smartc/SkyConditions_90640/Enclosure/Sky Conditions 90640 - Enclosure.3mf

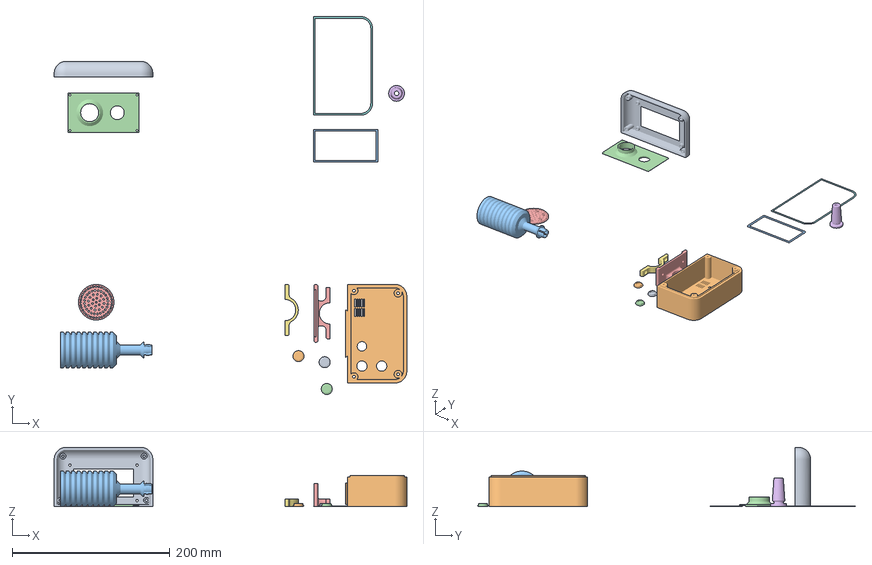
[picture p15: CAD file, 2026-04-03]
Enclosure/Sky Conditions 90640 - Enclosure.3mf
446.8 x 478.9 x 75.0 mm
Housing - Top.stl
Housing - Base.stl
Stevenson Screen.stl
Sensor Insert Plate.stl
Housing - Bracket.stl
TPU Cable Grommet.stl
Housing - Bracket Clamp.stl
TPU Housing Body Gasket.stl
Housing - Plug.stl x 3
TPU Sensor Insert Gasket.stl
Stevenson Screen - Base Cap.stl
