smartc/SkyConditions_90640/Enclosure/TPU Housing Body Gasket.stl

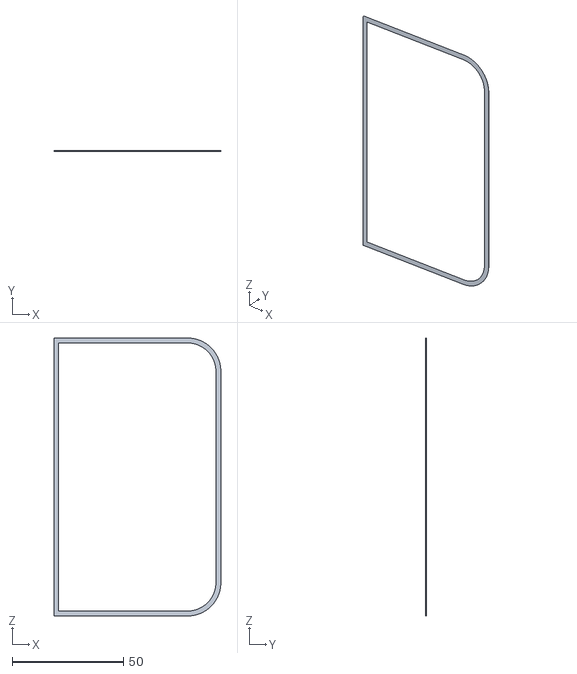
[picture p16: CAD file, 2026-04-03]
Enclosure/TPU Housing Body Gasket.stl
75.0 x 0.5 x 125.0
