smartc/SkyConditions_90640/html_templates.h

#ifndef HTML_TEMPLATES_H
#define HTML_TEMPLATES_H

#include <Arduino.h>
#include <WiFi.h>
#include "config.h"
#include "sky_sensor.h"
#include "config_store.h"
#include "rain_sensor.h"
#include "dht_sensor.h"

// ---------------------------------------------------------------------------
// Shared CSS
// ---------------------------------------------------------------------------
inline String getCommonStyles()
{
  return
    "* { box-sizing: border-box; }\n"
    "body { font-family: Arial, sans-serif; background: #1a1a2e; color: #e0e0e0; margin: 0; padding: 16px; }\n"
    "h1, h2 { color: #a0c4ff; }\n"
    "a { color: #74b9ff; text-decoration: none; }\n"
    "a:hover { text-decoration: underline; }\n"
    ".card { background: #16213e; border-radius: 8px; padding: 16px; margin-bottom: 16px;"
             " box-shadow: 0 2px 8px rgba(0,0,0,0.4); }\n"
    "table { border-collapse: collapse; width: 100%; }\n"
    "th, td { border: 1px solid #2d3561; padding: 8px; text-align: left; }\n"
    "th { background: #0f3460; }\n"
    ".nav { margin-bottom: 16px; }\n"
    ".nav a { display: inline-block; background: #0f3460; color: #e0e0e0; padding: 8px 14px;"
              " border-radius: 4px; margin-right: 8px; }\n"
    ".nav a:hover { background: #16213e; text-decoration: none; }\n"
    ".nav a.warn { background: #7f4f00; }\n"
    ".tbtn { display:inline-block; padding:6px 12px; margin:2px; border-radius:4px;"
             " background:#0f3460; color:#e0e0e0; cursor:pointer; border:none;"
             " font-size:0.85em; }\n"
    ".tbtn:hover { background:#1a4a8a; }\n"
    ".tbtn.act { background:#4a90d9; color:#fff; }\n"
    "#hist-status { font-size:0.8em; color:#636e72; margin-top:8px; }\n"
    ".btn { display: inline-block; padding: 8px 16px; border-radius: 4px; cursor: pointer;"
            " border: none; color: white; }\n"
    ".btn-danger { background: #c0392b; }\n"
    ".btn-danger:hover { background: #96281b; }\n"
    ".stat-grid { display: grid; grid-template-columns: repeat(auto-fit, minmax(140px,1fr));"
                 " gap: 12px; }\n"
    ".stat-box { background: #0f3460; border-radius: 6px; padding: 12px; text-align: center; }\n"
    ".stat-label { font-size: 0.75em; color: #74b9ff; text-transform: uppercase; letter-spacing: 1px; }\n"
    ".stat-value { font-size: 1.6em; font-weight: bold; margin-top: 4px; }\n"
    ".sky-temp  { color: #a29bfe; }\n"
    ".min-temp  { color: #74b9ff; }\n"
    ".max-temp  { color: #fd79a8; }\n"
    ".med-temp  { color: #55efc4; }\n"
    ".amb-temp  { color: #ffeaa7; }\n"
    "#thermal-canvas { display: block; margin: 0 auto; image-rendering: pixelated; border-radius: 4px; }\n"
    "#ws-status { font-size: 0.8em; color: #636e72; margin-top: 6px; text-align: center; }\n";
}

// ---------------------------------------------------------------------------
// Shared page header
// ---------------------------------------------------------------------------
inline String getPageHeader(const String& title)
{
  return
    "<!DOCTYPE html><html>\n"
    "<head><title>" + title + "</title>\n"
    "<meta charset='UTF-8'>\n"
    "<meta name='viewport' content='width=device-width, initial-scale=1'>\n"
    "<style>" + getCommonStyles() + "</style>\n"
    "</head>\n<body>\n";
}

// ---------------------------------------------------------------------------
// Navigation bar
// ---------------------------------------------------------------------------
inline String getNavBar()
{
  return
    "<div class='nav'>\n"
    "<a href='/'>Home</a>\n"
    "<a href='/setup'>Setup</a>\n"
    "<a href='/trends'>Trends</a>\n"
    "<a href='/console'>Console</a>\n"
    "<a href='/update' class='warn'>Update</a>\n"
    "</div>\n";
}

// ---------------------------------------------------------------------------
// Adaptive lux formatter – 1 dp when >= 1 lux, more below that.
// ---------------------------------------------------------------------------
inline String fmtLux(float lux)
{
  if (lux >= 1.0f)    return String(lux, 1)  + " lux";
  if (lux >= 0.1f)    return String(lux, 3)  + " lux";
  if (lux >= 0.001f)  return String(lux, 4)  + " lux";
  char buf[24]; snprintf(buf, sizeof(buf), "%.2e lux", lux); return String(buf);
}

// ---------------------------------------------------------------------------
// Home page – live thermal view + reading cards
// ---------------------------------------------------------------------------
inline String getHomePage()
{
  String ip   = WiFi.localIP().toString();
  String host = "ws://" + ip + ":81";

  String html = getPageHeader("Sky Conditions Monitor");
  html += "<h1>Sky Conditions Monitor</h1>\n";
  html += getNavBar();

  // Live thermal canvas
  html += "<div class='card'>\n";
  html += "<h2>Live Thermal View</h2>\n";
  html += "<canvas id='thermal-canvas' width='640' height='480'></canvas>\n";
  html += "<div id='ws-status'>Connecting...</div>\n";
  html += "</div>\n";

  // Temperature statistics
  html += "<div class='card'>\n";
  html += "<h2>Current Readings</h2>\n";
  html += "<div class='stat-grid'>\n";
  html += "  <div class='stat-box'><div class='stat-label'>Sky Temp<br>(center 50% FOV)</div>"
          "    <div class='stat-value sky-temp' id='sky-temp'>--</div></div>\n";
  html += "  <div class='stat-box'><div class='stat-label'>Frame Min</div>"
          "    <div class='stat-value min-temp' id='min-temp'>--</div></div>\n";
  html += "  <div class='stat-box'><div class='stat-label'>Frame Max</div>"
          "    <div class='stat-value max-temp' id='max-temp'>--</div></div>\n";
  html += "  <div class='stat-box'><div class='stat-label'>Frame Median</div>"
          "    <div class='stat-value med-temp' id='med-temp'>--</div></div>\n";
  {
    String ambSrc;
    if      (deviceConfig.dhtType == 5 && dhtData.valid) ambSrc = "BME280";
    else if (deviceConfig.dhtType == 4 && dhtData.valid) ambSrc = "BMP280";
    else if (deviceConfig.dhtType == 3 && dhtData.valid) ambSrc = "BMP180";
    else if (deviceConfig.dhtType && dhtData.valid)      ambSrc = "DHT";
    else                                                  ambSrc = "MLX die";
    html += "  <div class='stat-box'><div class='stat-label'>Ambient<br>"
            "<span style='font-size:0.8em;color:#8899aa' id='amb-src'>" + ambSrc + "</span></div>"
            "    <div class='stat-value amb-temp' id='amb-temp'>" +
            (skyConditions.hasData() ? String(skyConditions.getAmbientTemperature(), 1) + "°C" : "--") +
            "</div></div>\n";
  }
  if ((deviceConfig.dhtType >= 1 && deviceConfig.dhtType <= 2) || deviceConfig.dhtType == 5) {
    // Humidity available from DHT11/DHT22 and BME280
    const char *humSrc = (deviceConfig.dhtType == 5) ? "BME280" : "DHT";
    String humVal = dhtData.valid ? String(dhtData.humidity, 0) + "%" : "--";
    html += "  <div class='stat-box'><div class='stat-label'>Humidity<br>"
            "<span style='font-size:0.8em;color:#8899aa'>" + String(humSrc) + "</span></div>"
            "    <div class='stat-value' id='hum-val' style='color:#74b9ff'>" + humVal + "</div></div>\n";
  }
  if (deviceConfig.dhtType == 3 || deviceConfig.dhtType == 4 || deviceConfig.dhtType == 5) {
    // Pressure available from BMP180/BMP280/BME280
    const char *presSrc = (deviceConfig.dhtType == 5) ? "BME280"
                        : (deviceConfig.dhtType == 4) ? "BMP280" : "BMP180";
    String presVal = dhtData.valid ? String(dhtData.pressure, 1) + " hPa" : "--";
    html += "  <div class='stat-box'><div class='stat-label'>Pressure<br>"
            "<span style='font-size:0.8em;color:#8899aa'>" + String(presSrc) + "</span></div>"
            "    <div class='stat-value' id='pres-val' style='color:#74b9ff'>" + presVal + "</div></div>\n";
  }
  html += "  <div class='stat-box'><div class='stat-label'>Cloud Cover<br><span style='font-size:0.8em;color:#74b9ff'>Mean</span></div>"
          "    <div class='stat-value' id='cloud-mean' style='color:#dfe6e9'>" +
          (skyConditions.hasData() ? String(skyConditions.getCloudCoverMean(), 0) + "%" : "--") +
          "</div></div>\n";
  html += "  <div class='stat-box'><div class='stat-label'>Cloud Cover<br><span style='font-size:0.8em;color:#74b9ff'>Per-Pixel</span></div>"
          "    <div class='stat-value' id='cloud-px' style='color:#b2bec3'>" +
          (skyConditions.hasData() ? String(skyConditions.getCloudCoverPixel(), 0) + "%" : "--") +
          "</div></div>\n";
  html += "  <div class='stat-box'><div class='stat-label'>Sky Brightness</div>"
          "    <div class='stat-value' id='lux-val' style='color:#fdcb6e'>" +
          (skyConditions.hasBrightnessData() ? fmtLux(skyConditions.getLux()) : "--") +
          "</div></div>\n";
  html += "  <div class='stat-box'><div class='stat-label'>Sky Quality</div>"
          "    <div class='stat-value' id='sqm-val' style='color:#00cec9'>" +
          (skyConditions.hasBrightnessData() ? String(skyConditions.getSqm(), 2) + " mag/\"²" : "--") +
          "</div></div>\n";
  {
    bool enabled     = deviceConfig.rainEnabled;
    bool wet         = rainIsWet();
    bool relayMode   = (deviceConfig.rainMode == 0);
    String mainColor = !enabled ? "#636e72" : (wet ? "#74b9ff" : "#00b894");
    String mainLabel = !enabled ? "--"       : (wet ? "WET"     : "DRY");
    String subTxt;
    if (!enabled) {
      subTxt = "Disabled";
    } else if (relayMode) {
      subTxt = rainData.relayWet ? "Relay: WET" : "Relay: DRY";
    } else {
      subTxt = rainData.modbusOk
               ? (rainData.modbusWet ? "RS485: WET" : "RS485: DRY")
               : "RS485: --";
    }
    // IDs are used by the WebSocket text-message handler for live relay updates.
    html += "  <div class='stat-box'><div class='stat-label'>Rain / Snow<br>"
            "<span style='font-size:0.8em;color:#8899aa'>" +
            String(relayMode ? "Relay" : "RS485") + "</span></div>"
            "    <div class='stat-value' id='rain-state' style='color:" + mainColor + "'>" + mainLabel + "</div>"
            "    <div id='rain-sub' style='font-size:0.65em;color:#b2bec3;margin-top:4px'>" + subTxt + "</div></div>\n";
  }
  html += "</div>\n";  // stat-grid
  html += "</div>\n";  // card

  // Thermal snapshot image (auto-refreshes every JPEG_INTERVAL_MS)
  html += "<div class='card'>\n";
  html += "<h2>Thermal Snapshot</h2>\n";
  html += "<p style='font-size:0.8em;color:#636e72'>Refreshes every " +
          String(JPEG_INTERVAL_MS / 1000) + " s &nbsp;&middot;&nbsp; "
          "<a href='/thermal.jpg'>direct link</a></p>\n";
  html += "<img id='thermal-snap' src='/thermal.jpg' "
          "style='display:block;margin:0 auto;max-width:100%;border-radius:4px;'>\n";
  html += "</div>\n";

  // Device info
  html += "<div class='card'>\n";
  html += "<h2>Device Information</h2>\n";
  html += "<table><tr><th>Property</th><th>Value</th></tr>\n";
  html += "<tr><td>Device Name</td><td>" + String(DEVICE_NAME)    + "</td></tr>\n";
  html += "<tr><td>Firmware</td><td>"    + String(MANUFACTURER_V) + "</td></tr>\n";
  html += "<tr><td>IP Address</td><td>"  + ip + "</td></tr>\n";
  html += "<tr><td>MAC Address</td><td>" + WiFi.macAddress()        + "</td></tr>\n";
  html += "<tr><td>SSID</td><td>"        + WiFi.SSID()              + "</td></tr>\n";
  html += "<tr><td>Signal</td><td>"      + String(WiFi.RSSI())      + " dBm</td></tr>\n";
  html += "<tr><td>ASCOM Port</td><td>"  + String(ALPACA_PORT)      + "</td></tr>\n";
  html += "<tr><td>Uptime</td><td><span id='uptime' data-s='" +
          String(millis()/1000) + "'></span></td></tr>\n";
  html += "<tr><td>Free Heap</td><td>"   + String(ESP.getFreeHeap()) + " bytes</td></tr>\n";
  html += "</table>\n";
  html += "</div>\n";

  // ---------------------------------------------------------------------------
  // JavaScript – WebSocket client + jet colormap renderer
  // ---------------------------------------------------------------------------

  // Compute the box region that matches the per-pixel cloud cover region.
  // Both cloud cover methods are always computed; the box always tracks the
  // per-pixel region (which equals center FOV when cloudPixelRegion == 0).
  int boxCCS, boxCCE, boxCRS, boxCRE;
  if (deviceConfig.cloudPixelRegion == 1) {
    int edge = (int)deviceConfig.cloudEdgeExclude;
    boxCCS = edge;
    boxCCE = SENSOR_COLS - 1 - edge;
    boxCRS = edge;
    boxCRE = SENSOR_ROWS - 1 - edge;
    if (boxCRS > boxCRE || boxCCS > boxCCE) { // degenerate – fall back
      boxCCS = CENTER_COL_START; boxCCE = CENTER_COL_END;
      boxCRS = CENTER_ROW_START; boxCRE = CENTER_ROW_END;
    }
  } else {
    boxCCS = CENTER_COL_START; boxCCE = CENTER_COL_END;
    boxCRS = CENTER_ROW_START; boxCRE = CENTER_ROW_END;
  }

  html += R"rawjs(
<script>
const COLS = 32, ROWS = 24, PIXELS = 768;
const HEADER = 16;  // bytes: 4×float32 (min, max, median, skyTemp)
const canvas = document.getElementById('thermal-canvas');
const ctx    = canvas.getContext('2d');
const imgData = ctx.createImageData(COLS, ROWS);
const status  = document.getElementById('ws-status');

// ClearDarkSky colormap: t=0 (coldest/clear) → dark navy, t=1 (warmest/overcast) → white
const CDS_STOPS = [
  [0,62,126],[19,83,147],[38,102,166],[78,142,206],[98,162,226],
  [118,182,246],[153,217,217],[173,237,237],[193,193,193],[233,233,233],[250,250,250]
];
function cds(t) {
  if (t <= 0) return CDS_STOPS[0];
  if (t >= 1) return CDS_STOPS[10];
  const lo = Math.floor(t * 10);
  const f  = t * 10 - lo;
  return CDS_STOPS[lo].map((c, i) => Math.round(c + f * (CDS_STOPS[lo+1][i] - c)));
}

// Pre-compute colormap lookup table
const skyLT = new Array(256);
for (let i = 0; i < 256; i++) { skyLT[i] = cds(i/255); }

function fmtLux(lux) {
  if (lux >= 1)     return lux.toFixed(1)       + ' lux';
  if (lux >= 0.1)   return lux.toFixed(3)       + ' lux';
  if (lux >= 0.001) return lux.toFixed(4)       + ' lux';
  return lux.toExponential(2) + ' lux';
}

// Pre-allocate the offscreen source canvas; reused every frame to avoid GC churn.
const srcCanvas = new OffscreenCanvas(COLS, ROWS);
const srcCtx    = srcCanvas.getContext('2d');

let ws, fpsCount = 0, lastFpsTime = Date.now(), fps = 0;

function connect() {
  ws = new WebSocket(')rawjs" + host + R"rawjs(');
  ws.binaryType = 'arraybuffer';

  ws.onopen    = () => { status.textContent = 'Connected'; };
  ws.onclose   = () => { status.textContent = 'Disconnected – reconnecting…';
                          setTimeout(connect, 1500); };
  ws.onerror   = () => { ws.close(); };

  ws.onmessage = (evt) => {
    // Text messages carry JSON status updates.
    if (typeof evt.data === 'string') {
      try {
        const d = JSON.parse(evt.data);
        // Rain state (relay mode live update)
        if (d.rain !== undefined) {
          const wet = d.rain === 'WET';
          const el  = document.getElementById('rain-state');
          const sub = document.getElementById('rain-sub');
          if (el)  { el.textContent = d.rain; el.style.color = wet ? '#74b9ff' : '#00b894'; }
          if (sub) sub.textContent = wet ? 'Relay: WET' : 'Relay: DRY';
        }
        // Sensor state (cloud cover, brightness, ambient)
        if (d.amb !== undefined) {
          const nd = d.has_data, nb = d.has_brightness;
          document.getElementById('amb-temp').textContent   = nd ? d.amb.toFixed(1)        + '°C'        : '--';
          document.getElementById('cloud-mean').textContent = nd ? d.cloud_mean.toFixed(0) + '%'         : '--';
          document.getElementById('cloud-px').textContent   = nd ? d.cloud_px.toFixed(0)   + '%'         : '--';
          document.getElementById('lux-val').textContent    = nb ? fmtLux(d.lux)                         : '--';
          document.getElementById('sqm-val').textContent    = nb ? d.sqm.toFixed(2)        + ' mag/″²'   : '--';
          const humEl = document.getElementById('hum-val');
          if (humEl) humEl.textContent = (d.dht_hum !== undefined) ? d.dht_hum.toFixed(0) + '%' : '--';
        }
      } catch(e) {}
      return;
    }
    // Binary messages are thermal frames.
    const buf  = evt.data;
    if (buf.byteLength < HEADER + PIXELS) return;

    const dv   = new DataView(buf);
    const minT = dv.getFloat32(0,  true);
    const maxT = dv.getFloat32(4,  true);
    const medT = dv.getFloat32(8,  true);
    const skyT = dv.getFloat32(12, true);
    const pix  = new Uint8Array(buf, HEADER, PIXELS);

    // Render pixels
    for (let i = 0; i < PIXELS; i++) {
      const [r,g,b] = skyLT[pix[i]];
      imgData.data[i*4]   = r;
      imgData.data[i*4+1] = g;
      imgData.data[i*4+2] = b;
      imgData.data[i*4+3] = 255;
    }

    // Scale 32×24 → 640×480 with bicubic interpolation to smooth pixels and
    // reduce MLX90640 row/column banding artifacts in the live view.
    srcCtx.putImageData(imgData, 0, 0);
    ctx.imageSmoothingEnabled = true;
    ctx.imageSmoothingQuality = 'high';
    ctx.drawImage(srcCanvas, 0, 0, canvas.width, canvas.height);

    // Draw cloud cover region box
    const ccs = )rawjs" + String(boxCCS) + R"rawjs(,
          cce = )rawjs" + String(boxCCE + 1) + R"rawjs(,
          crs = )rawjs" + String(boxCRS) + R"rawjs(,
          cre = )rawjs" + String(boxCRE + 1) + R"rawjs(;
    const scaleX = canvas.width  / COLS;
    const scaleY = canvas.height / ROWS;
    ctx.strokeStyle = 'rgba(255,60,60,0.85)';
    ctx.lineWidth   = 2;
    ctx.strokeRect(ccs*scaleX, crs*scaleY,
                   (cce-ccs)*scaleX, (cre-crs)*scaleY);

    // Update stat readouts
    document.getElementById('sky-temp').textContent = skyT.toFixed(1) + '°C';
    document.getElementById('min-temp').textContent = minT.toFixed(1) + '°C';
    document.getElementById('max-temp').textContent = maxT.toFixed(1) + '°C';
    document.getElementById('med-temp').textContent = medT.toFixed(1) + '°C';

    // FPS
    fpsCount++;
    const now = Date.now();
    if (now - lastFpsTime >= 1000) {
      fps = fpsCount;
      fpsCount = 0;
      lastFpsTime = now;
    }
    status.textContent =
      'Live – ' + fps + ' fps | Sky: ' + skyT.toFixed(1) +
      '°C | Min: ' + minT.toFixed(1) + '°C | Max: ' + maxT.toFixed(1) + '°C';
  };
}

connect();

// Real-time uptime counter.
(function() {
  const el = document.getElementById('uptime');
  if (!el) return;
  let sec = parseInt(el.dataset.s, 10);
  function fmt(s) {
    const d = Math.floor(s / 86400);
    const h = Math.floor(s % 86400 / 3600);
    const m = Math.floor(s % 3600 / 60);
    const ss = s % 60;
    if (d > 0) return d + 'd ' + h + 'h ' + m + 'm';
    if (h > 0) return h + 'h ' + m + 'm ' + ss + 's';
    return m + 'm ' + ss + 's';
  }
  el.textContent = fmt(sec);
  setInterval(function() { el.textContent = fmt(++sec); }, 1000);
})();

// Auto-refresh the static JPEG snapshot.
setInterval(() => {
  const img = document.getElementById('thermal-snap');
  if (img) img.src = '/thermal.jpg?' + Date.now();
}, )rawjs" + String(JPEG_INTERVAL_MS) + R"rawjs();
</script>
)rawjs";

  html += "</body></html>";
  return html;
}

// ---------------------------------------------------------------------------
// Setup page
// ---------------------------------------------------------------------------
inline String getSetupPage()
{
  String html = getPageHeader("Sky Conditions Setup");
  html += "<h1>Sky Conditions Setup</h1>\n";
  html += getNavBar();

  // Current readings snapshot
  html += "<div class='card'>\n";
  html += "<h2>Current Status</h2>\n";
  html += "<table><tr><th>Property</th><th>Value</th></tr>\n";
  if (skyConditions.hasData()) {
    html += "<tr><td>Sky Temperature (center 50% FOV)</td><td>" +
            String(skyConditions.getSkyTemperature(), 2) + " °C</td></tr>\n";
    html += "<tr><td>Frame Minimum</td><td>" +
            String(skyConditions.getMinTemperature(), 2) + " °C</td></tr>\n";
    html += "<tr><td>Frame Maximum</td><td>" +
            String(skyConditions.getMaxTemperature(), 2) + " °C</td></tr>\n";
    html += "<tr><td>Frame Median</td><td>" +
            String(skyConditions.getMedianTemperature(), 2) + " °C</td></tr>\n";
    html += "<tr><td>Ambient (die temp)</td><td>" +
            String(skyConditions.getAmbientTemperature(), 2) + " °C</td></tr>\n";
    unsigned long ageSec = (millis() - skyConditions.getLastUpdateMillis()) / 1000;
    html += "<tr><td>Last Update (thermal)</td><td>" + String(ageSec) + " s ago</td></tr>\n";
  } else {
    html += "<tr><td colspan='2'>No sensor data yet</td></tr>\n";
  }
  if (skyConditions.hasBrightnessData()) {
    html += "<tr><td>Sky Brightness</td><td>" +
            String(skyConditions.getLux(), 4) + " lux</td></tr>\n";
    html += "<tr><td>Sky Quality</td><td>" +
            String(skyConditions.getSqm(), 2) + " mag/arcsec\u00B2</td></tr>\n";
    unsigned long bAgeSec = (millis() - skyConditions.getLastBrightnessMillis()) / 1000;
    html += "<tr><td>Last Update (brightness)</td><td>" + String(bAgeSec) + " s ago</td></tr>\n";
  } else {
    html += "<tr><td>Sky Brightness</td><td>No TSL2591 data yet</td></tr>\n";
  }
  html += "</table>\n";
  html += "</div>\n";

  // ASCOM information
  html += "<div class='card'>\n";
  html += "<h2>ASCOM Alpaca</h2>\n";
  html += "<table><tr><th>Property</th><th>Value</th></tr>\n";
  html += "<tr><td>Device Type</td><td>ObservingConditions</td></tr>\n";
  html += "<tr><td>Device Number</td><td>0</td></tr>\n";
  html += "<tr><td>Alpaca Port</td><td>" + String(ALPACA_PORT) + "</td></tr>\n";
  html += "<tr><td>Discovery Port</td><td>" + String(ALPACA_DISCOVERY_PORT) + "</td></tr>\n";
  html += "<tr><td>API Base URL</td><td>http://" + WiFi.localIP().toString() +
          ":" + String(ALPACA_PORT) + "/api/v1/observingconditions/0</td></tr>\n";
  html += "<tr><td>Implemented Sensors</td><td>SkyTemperature, Temperature, SkyBrightness, SkyQuality, CloudCover</td></tr>\n";
  html += "</table>\n";
  html += "</div>\n";

  // Hardware information
  html += "<div class='card'>\n";
  html += "<h2>Hardware</h2>\n";
  html += "<table><tr><th>Property</th><th>Value</th></tr>\n";
  html += "<tr><td>Sensor</td><td>MLX90640 (" +
          String(SENSOR_COLS) + "×" + String(SENSOR_ROWS) + " pixels)</td></tr>\n";
  html += "<tr><td>I2C SDA Pin</td><td>" + String(THERMAL_SDA_PIN) + "</td></tr>\n";
  html += "<tr><td>I2C SCL Pin</td><td>" + String(THERMAL_SCL_PIN) + "</td></tr>\n";
  html += "<tr><td>I2C Frequency</td><td>" + String(THERMAL_I2C_FREQ/1000) + " kHz</td></tr>\n";
  html += "<tr><td>Frame Rate</td><td>" + String(1000/FRAME_INTERVAL_MS) + " Hz</td></tr>\n";
  html += "<tr><td>Center FOV Region</td><td>Cols " +
          String(CENTER_COL_START) + "–" + String(CENTER_COL_END) + ", Rows " +
          String(CENTER_ROW_START) + "–" + String(CENTER_ROW_END) + " (" +
          String(CENTER_PIXEL_COUNT) + " pixels)</td></tr>\n";
  html += "<tr><td>ESP32 Free Heap</td><td>" + String(ESP.getFreeHeap()) + " bytes</td></tr>\n";
  html += "</table>\n";
  html += "</div>\n";

  // Calibration / config
  html += "<div class='card'>\n";
  html += "<h2>Calibration</h2>\n";
  html += "<p style='font-size:0.85em;color:#8899aa'>Settings are saved persistently in NVS flash.</p>\n";
  html += "<form action='/save_config' method='POST'>\n";
  html += "<table><tr><th>Parameter</th><th>Value</th><th>Description</th></tr>\n";

  String inpStyle = "width:90px;background:#1a1a2e;color:#e0e0e0;"
                    "border:1px solid #2d3561;border-radius:4px;padding:4px;";

  // ── Calibration ─────────────────────────────────────────────────────────
  html += "<tr><th colspan='3' style='background:#0a2a50'>Calibration</th></tr>\n";

  html += "<tr><td>SQM Offset (mag/arcsec\u00B2)</td>"
          "<td><input type='number' name='sqmOffset' step='0.01' value='" +
          String(deviceConfig.sqmOffset, 2) + "' style='" + inpStyle + "'></td>"
          "<td>Additive correction applied to the calculated SQM value</td></tr>\n";

  html += "<tr><td>SQM Reference (lux)</td>"
          "<td><input type='number' name='sqmRef' step='1' min='1' value='" +
          String(deviceConfig.sqmReference, 0) + "' style='" + inpStyle + "'></td>"
          "<td>Lux level that maps to SQM\u202F0.0 (default\u202F108000)</td></tr>\n";

  html += "<tr><td>Cloud-Clear Delta (\u00B0C)</td>"
          "<td><input type='number' name='cloudClear' step='0.5' value='" +
          String(deviceConfig.cloudClearDelta, 1) + "' style='" + inpStyle + "'></td>"
          "<td>Ambient \u2212 Sky \u2265 this \u2192 0\u202F% cloud cover (clear)</td></tr>\n";

  html += "<tr><td>Cloud-Overcast Delta (\u00B0C)</td>"
          "<td><input type='number' name='cloudOvercast' step='0.5' value='" +
          String(deviceConfig.cloudOvercastDelta, 1) + "' style='" + inpStyle + "'></td>"
          "<td>Ambient \u2212 Sky \u2264 this \u2192 100\u202F% cloud cover (overcast)</td></tr>\n";

  // ── Imaging ──────────────────────────────────────────────────────────────
  html += "<tr><th colspan='3' style='background:#0a2a50'>Imaging</th></tr>\n";

  html += "<tr><td>Snapshot Interval (s)</td>"
          "<td><input type='number' name='snapSec' min='5' max='3600' step='5' value='" +
          String(deviceConfig.snapshotIntervalSec) + "' style='" + inpStyle + "'></td>"
          "<td>How often /thermal.jpg is regenerated (seconds)</td></tr>\n";

  html += "<tr><td>JPEG Quality (0\u2013100)</td>"
          "<td><input type='number' name='jpegQuality' min='1' max='100' step='1' value='" +
          String(deviceConfig.jpegQuality) + "' style='" + inpStyle + "'></td>"
          "<td>Higher = better image, larger file</td></tr>\n";

  // ── Brightness sensor ─────────────────────────────────────────────────────
  html += "<tr><th colspan='3' style='background:#0a2a50'>Brightness Sensor (TSL2591)</th></tr>\n";

  {
    const char* timingLabels[] = {"100 ms","200 ms","300 ms (default)","400 ms","500 ms","600 ms"};
    html += "<tr><td>Integration Time</td><td>";
    html += "<select name='tslInteg' style='" + inpStyle + "'>";
    for (int i = 0; i < 6; i++) {
      html += "<option value='" + String(i) + "'";
      if (deviceConfig.tsl2591Integration == i) html += " selected";
      html += ">" + String(timingLabels[i]) + "</option>";
    }
    html += "</select></td><td>Longer integration improves dark-sky sensitivity</td></tr>\n";
  }

  // ── ASCOM ─────────────────────────────────────────────────────────────────
  html += "<tr><th colspan='3' style='background:#0a2a50'>ASCOM</th></tr>\n";

  html += "<tr><td>Average Period (s)</td>"
          "<td><input type='number' name='avgPeriod' min='0' step='0.1' value='" +
          String(deviceConfig.averagePeriod, 1) + "' style='" + inpStyle + "'></td>"
          "<td>ObservingConditions AveragePeriod; persisted across reboots</td></tr>\n";

  html += "<tr><td>Cloud Cover Method<br><span style='font-size:0.8em;color:#8899aa'>(Alpaca reporting)</span></td><td>";
  html += "<select name='cloudMethod' style='" + inpStyle + "width:130px;'>";
  html += "<option value='0'" + String(deviceConfig.cloudCoverMethod == 0 ? " selected" : "") +
          ">Mean (FOV avg)</option>";
  html += "<option value='1'" + String(deviceConfig.cloudCoverMethod == 1 ? " selected" : "") +
          ">Per-pixel</option>";
  html += "</select></td>"
          "<td>Which calculation to report via ASCOM Alpaca CloudCover. "
          "Both are always recorded in history and shown on the home page.</td></tr>\n";

  html += "<tr><td>Per-Pixel Region</td><td>";
  html += "<select name='cloudPxRgn' id='cloudPxRgn' style='" + inpStyle + "width:130px;'"
          " onchange='updateEdge()'>";
  html += "<option value='0'" + String(deviceConfig.cloudPixelRegion == 0 ? " selected" : "") +
          ">Centre FOV</option>";
  html += "<option value='1'" + String(deviceConfig.cloudPixelRegion == 1 ? " selected" : "") +
          ">Full Frame</option>";
  html += "</select></td>"
          "<td>Pixel region used for the per-pixel cloud cover calculation</td></tr>\n";

  html += "<tr><td>Edge Exclusion (pixels)<br><span style='font-size:0.8em;color:#8899aa'>(Full Frame only)</span></td><td>";
  html += "<input type='number' name='cloudEdge' id='cloudEdge' min='0' max='10' step='1' value='" +
          String(deviceConfig.cloudEdgeExclude) + "' style='" + inpStyle + "'"  +
          String(deviceConfig.cloudPixelRegion == 0 ? " disabled" : "") + "></td>"
          "<td>Pixels to ignore on each side of the frame (0\u201310). "
          "With default 2: uses " +
          String((SENSOR_COLS - 4)) + "\u00D7" + String((SENSOR_ROWS - 4)) + " = " +
          String((SENSOR_COLS - 4) * (SENSOR_ROWS - 4)) + " pixels</td></tr>\n";

  html += R"rawsetup(
<script>
function updateEdge() {
  var rgn = document.getElementById('cloudPxRgn').value;
  document.getElementById('cloudEdge').disabled = (rgn === '0');
}
</script>
)rawsetup";

  // ── Rain Sensor ───────────────────────────────────────────────────────────
  html += "<tr><th colspan='3' style='background:#0a2a50'>Rain Sensor"
          " <span style='font-weight:normal;font-size:0.8em;color:#74b9ff'>"
          "(takes effect after reboot)</span></th></tr>\n";
  html += "<tr><td>Rain Sensor</td><td>"
          "<label style='cursor:pointer'>"
          "<input type='checkbox' name='rainEnabled' value='1'" +
          String(deviceConfig.rainEnabled ? " checked" : "") +
          "> Enabled</label></td>"
          "<td>Uncheck to disable the rain sensor entirely (e.g. on XIAO Sense which lacks rain sensor hardware).</td></tr>\n";
  html += "<tr><td>Sensor Mode</td><td>";
  html += "<select name='rainMode' style='" + inpStyle + "width:140px;'>";
  html += "<option value='0'" + String(deviceConfig.rainMode == 0 ? " selected" : "") +
          ">Relay</option>";
  html += "<option value='1'" + String(deviceConfig.rainMode == 1 ? " selected" : "") +
          ">RS485 Modbus</option>";
  html += "</select></td>"
          "<td>Relay: senses relay contact closure via GPIO. "
          "RS485: polls ZTS-3000 via Modbus RTU.</td></tr>\n";

  // ── Ambient Temperature Sensor ───────────────────────────────────────────
  html += "<tr><th colspan='3' style='background:#0a2a50'>Ambient Temperature Sensor"
          " <span style='font-weight:normal;font-size:0.8em;color:#74b9ff'>"
          "(takes effect after reboot)</span></th></tr>\n";
  html += "<tr><td>Sensor Type</td><td>";
  html += "<select name='dhtType' style='" + inpStyle + "width:120px;'"
          " onchange=\"var s=(this.value=='4'||this.value=='5');document.getElementById('bmp280AddrRow').style.display=(s?'':'none')\">";
  html += "<option value='0'" + String(deviceConfig.dhtType == 0 ? " selected" : "") + ">Disabled</option>";
  html += "<option value='1'" + String(deviceConfig.dhtType == 1 ? " selected" : "") + ">DHT11</option>";
  html += "<option value='2'" + String(deviceConfig.dhtType == 2 ? " selected" : "") + ">DHT22</option>";
  html += "<option value='3'" + String(deviceConfig.dhtType == 3 ? " selected" : "") + ">BMP180</option>";
  html += "<option value='4'" + String(deviceConfig.dhtType == 4 ? " selected" : "") + ">BMP280</option>";
  html += "<option value='5'" + String(deviceConfig.dhtType == 5 ? " selected" : "") + ">BME280</option>";
  html += "</select></td>"
          "<td>Replaces MLX die temperature with true external ambient for cloud-cover calculations. "
          "DHT11/DHT22: on D7 (GPIO44), also expose Humidity via Alpaca. "
          "DHT11: ±2°C. &nbsp; DHT22: ±0.5°C. &nbsp; "
          "<b>BMP180</b>: ±0.5°C, I2C addr 0x77. &nbsp; "
          "<b>BMP280</b>: ±0.5°C, temp+pressure, I2C addr selectable below. &nbsp; "
          "<b>BME280</b>: ±0.5°C, temp+pressure+humidity, I2C addr selectable below. "
          "BMP/BME sensors share the SDA/SCL bus. Takes effect after reboot.</td></tr>\n";
  html += "<tr id='bmp280AddrRow' style='" + String((deviceConfig.dhtType == 4 || deviceConfig.dhtType == 5) ? "" : "display:none;") + "'>";
  html += "<td>BMP280 Address</td><td>";
  html += "<select name='bmp280Addr' style='" + inpStyle + "width:120px;'>";
  html += "<option value='118'" + String(deviceConfig.bmp280Addr == 0x76 ? " selected" : "") + ">0x76 (SDO&rarr;GND)</option>";
  html += "<option value='119'" + String(deviceConfig.bmp280Addr == 0x77 ? " selected" : "") + ">0x77 (SDO&rarr;VCC)</option>";
  html += "</select></td>"
          "<td>SDO pin tied to GND &rarr; 0x76 (common default). "
          "SDO pin tied to VCC &rarr; 0x77. Check your module's silkscreen or datasheet. "
          "Takes effect after reboot.</td></tr>\n";

  // ── Identity ──────────────────────────────────────────────────────────────
  html += "<tr><th colspan='3' style='background:#0a2a50'>Identity</th></tr>\n";

  html += "<tr><td>Location</td>"
          "<td><input type='text' name='location' maxlength='31' value='" +
          String(deviceConfig.location) + "' style='" + inpStyle + "width:180px;'></td>"
          "<td>Appears in Alpaca management API discovery response</td></tr>\n";

  // ── Network ────────────────────────────────────────────────────────────────
  html += "<tr><th colspan='3' style='background:#0a2a50'>Network</th></tr>\n";

  html += "<tr><td>NTP Server</td>"
          "<td><input type='text' name='ntpServer' maxlength='63' value='" +
          String(deviceConfig.ntpServer) + "' style='" + inpStyle + "width:180px;' placeholder='e.g. 192.168.1.1'></td>"
          "<td>Preferred NTP server (blank = use pool.ntp.org / time.nist.gov). "
          "Takes effect after reboot.</td></tr>\n";

  // ── MQTT / Home Assistant ──────────────────────────────────────────────────
  html += "<tr><th colspan='3' style='background:#0a2a50'>MQTT / Home Assistant"
          " <span style='font-weight:normal;font-size:0.8em;color:#74b9ff'>"
          "(takes effect after reboot)</span></th></tr>\n";

  html += "<tr><td>Enable MQTT</td>"
          "<td><input type='checkbox' name='mqttEnabled' value='1'" +
          String(deviceConfig.mqttEnabled ? " checked" : "") + "></td>"
          "<td>Publish sensor data and Home Assistant autodiscovery</td></tr>\n";

  html += "<tr><td>Broker Address</td>"
          "<td><input type='text' name='mqttServer' maxlength='63' value='" +
          String(deviceConfig.mqttServer) + "' style='" + inpStyle + "width:180px;' placeholder='192.168.1.x'></td>"
          "<td>MQTT broker hostname or IP</td></tr>\n";

  html += "<tr><td>Broker Port</td>"
          "<td><input type='number' name='mqttPort' min='1' max='65535' value='" +
          String(deviceConfig.mqttPort) + "' style='" + inpStyle + "width:80px;'></td>"
          "<td>Default: 1883</td></tr>\n";

  html += "<tr><td>Username</td>"
          "<td><input type='text' name='mqttUser' maxlength='31' value='" +
          String(deviceConfig.mqttUser) + "' style='" + inpStyle + "width:160px;' placeholder='(optional)'></td>"
          "<td>Leave blank if broker requires no auth</td></tr>\n";

  html += "<tr><td>Password</td>"
          "<td><input type='password' name='mqttPass' maxlength='63' value='" +
          String(deviceConfig.mqttPassword) + "' style='" + inpStyle + "width:160px;' placeholder='(optional)'></td>"
          "<td></td></tr>\n";

  html += "<tr><td>Topic Prefix</td>"
          "<td><input type='text' name='mqttTopicPfx' maxlength='63' value='" +
          String(deviceConfig.mqttTopicPrefix) + "' style='" + inpStyle + "width:200px;'></td>"
          "<td>Default '<code>skyconditions</code>' auto-appends MAC suffix. "
          "State topic: <code>&lt;prefix&gt;/state</code></td></tr>\n";

  html += "</table>\n";
  html += "<br><input type='submit' value='Save Configuration' class='btn' style='background:#0f3460'>\n";
  html += "</form>\n";
  html += "</div>\n";

  // WiFi
  html += "<div class='card'>\n";
  html += "<h2>WiFi</h2>\n";
  html += "<p>SSID: <strong>" + WiFi.SSID() + "</strong> &nbsp;"
          " IP: <strong>" + WiFi.localIP().toString() + "</strong> &nbsp;"
          " Signal: <strong>" + String(WiFi.RSSI()) + " dBm</strong></p>\n";

  // Scan + connect form
  html += "<div style='margin-bottom:10px'>\n";
  html += "  <button id='wifi-scan-btn' class='btn' style='background:#0f3460'"
          " onclick='wifiScan()'>Scan for Networks</button>\n";
  html += "  <select id='wifi-sel' style='display:none;margin-left:8px;" +
          inpStyle + "width:250px' onchange='wifiSelChanged()'>"
          "<option value=''>-- select --</option></select>\n";
  html += "</div>\n";
  html += "<div style='margin-bottom:8px'>\n";
  html += "  <label style='display:inline-block;width:80px'>SSID</label>"
          "<input type='text' id='wifi-ssid' style='" + inpStyle + "width:250px'"
          " placeholder='Network name'>\n";
  html += "</div>\n";
  html += "<div style='margin-bottom:12px'>\n";
  html += "  <label style='display:inline-block;width:80px'>Password</label>"
          "<input type='password' id='wifi-pass' style='" + inpStyle + "width:250px'"
          " placeholder='Leave blank if open'>\n";
  html += "</div>\n";
  html += "<button class='btn' style='background:#0f3460' onclick='wifiConnect()'>Change WiFi</button>"
          " <span id='wifi-msg' style='font-size:0.9em;margin-left:8px'></span>\n";

  html += "<hr style='margin:16px 0;border-color:#1e3a5f'>\n";
  html += "<button class='btn btn-danger' onclick='resetWifi()'>Reset WiFi Settings</button>"
          " <span style='font-size:0.8em;color:#636e72;margin-left:8px'>"
          "Clears credentials and reboots into setup AP (SkyCond-Setup)</span>\n";

  html += R"rawwifi(
<script>
async function wifiScan() {
  const btn = document.getElementById('wifi-scan-btn');
  btn.textContent = 'Scanning\u2026'; btn.disabled = true;
  try {
    const nets = await fetch('/wifi/scan').then(r => r.json());
    const sel = document.getElementById('wifi-sel');
    sel.innerHTML = '<option value="">-- select --</option>';
    nets.sort((a,b) => b.rssi - a.rssi).forEach(n => {
      const o = document.createElement('option');
      o.value = n.ssid;
      o.textContent = n.ssid + '  (' + n.rssi + ' dBm' + (n.open ? ', open' : '') + ')';
      sel.appendChild(o);
    });
    sel.style.display = '';
  } catch(e) { alert('Scan failed – try again'); }
  btn.textContent = 'Scan for Networks'; btn.disabled = false;
}
function wifiSelChanged() {
  const v = document.getElementById('wifi-sel').value;
  if (v) document.getElementById('wifi-ssid').value = v;
}
async function wifiConnect() {
  const ssid = document.getElementById('wifi-ssid').value.trim();
  const pass = document.getElementById('wifi-pass').value;
  const msg  = document.getElementById('wifi-msg');
  if (!ssid) { msg.textContent = 'Enter an SSID.'; return; }
  if (!confirm('Connect to "' + ssid + '"?\nThe device will reconnect – your browser connection may be briefly interrupted.')) return;
  msg.textContent = 'Connecting\u2026';
  try {
    await fetch('/wifi/connect', {
      method: 'POST',
      headers: {'Content-Type': 'application/x-www-form-urlencoded'},
      body: 'ssid=' + encodeURIComponent(ssid) + '&password=' + encodeURIComponent(pass)
    });
  } catch(e) {}
  msg.textContent = 'Connecting to "' + ssid + '"\u2026 If the IP changes, reconnect at the new address. If it fails, use Reset WiFi Settings below.';
}
function resetWifi() {
  if (!confirm('Reset WiFi? The device will restart and create a setup AP.')) return;
  fetch('/reset_wifi', {method:'POST'})
    .then(() => alert('Resetting. Connect to WiFi AP: SkyCond-Setup'))
    .catch(() => alert('Request sent'));
}
function rebootDevice() {
  if (!confirm('Reboot the device?')) return;
  fetch('/reboot', {method:'POST'})
    .then(() => alert('Rebooting. Page will reload in 10 seconds.'))
    .catch(() => alert('Request sent'));
  setTimeout(() => location.reload(), 10000);
}
</script>
)rawwifi";
  html += "</div>\n";

  // Reboot
  html += "<div class='card'>\n";
  html += "<h2>Device</h2>\n";
  html += "<button class='btn btn-danger' onclick='rebootDevice()'>Reboot Device</button>\n";
  html += "</div>\n";

  html += "</body></html>";
  return html;
}

// ---------------------------------------------------------------------------
// Trends page – time-series charts for temperature and brightness
// ---------------------------------------------------------------------------
inline String getTrendsPage(bool rainEnabled)
{
  String html = getPageHeader("Sky Conditions – Trends");
  html += "<h1>Sky Conditions – Trends</h1>\n";
  html += getNavBar();

  // Time-range selector card
  html += "<div class='card'>\n";
  html += "<div>\n";
  html += "  <button class='tbtn' onclick='setRange(5,this)'>5 min</button>\n";
  html += "  <button class='tbtn' onclick='setRange(30,this)'>30 min</button>\n";
  html += "  <button class='tbtn act' onclick='setRange(60,this)'>1 hour</button>\n";
  html += "  <button class='tbtn' onclick='setRange(120,this)'>2 hours</button>\n";
  html += "  <button class='tbtn' onclick='setRange(360,this)'>6 hours</button>\n";
  html += "  <button class='tbtn' onclick='setRange(720,this)'>12 hours</button>\n";
  html += "  <button class='tbtn' onclick='setRange(1440,this)'>24 hours</button>\n";
  html += "</div>\n";
  html += "<div id='hist-status'>Loading...</div>\n";
  html += "</div>\n";

  // Chart canvases
  html += "<div class='card'><h2>Temperature (\u00B0C)</h2>"
          "<canvas id='cT' height='210' style='width:100%;display:block'></canvas></div>\n";
  html += "<div class='card'><h2>Cloud Cover (%)</h2>"
          "<canvas id='cC' height='170' style='width:100%;display:block'></canvas></div>\n";
  html += "<div class='card'><h2>Sky Brightness (lux)</h2>"
          "<canvas id='cL' height='170' style='width:100%;display:block'></canvas></div>\n";
  html += "<div class='card'><h2>Sky Quality (mag/arcsec\u00B2)</h2>"
          "<canvas id='cQ' height='170' style='width:100%;display:block'></canvas></div>\n";

  if (rainEnabled)
    html += "<div class='card'><h2>Rain / Snow</h2>"
            "<canvas id='cR' height='80' style='width:100%;display:block'></canvas></div>\n";

  html += R"rawjs(
<script>
// ── State ──────────────────────────────────────────────────────────────────
let curMinutes = 60;

function setRange(m, btn) {
  curMinutes = m;
  document.querySelectorAll('.tbtn').forEach(b => b.classList.remove('act'));
  btn.classList.add('act');
  loadData();
}

// ── Data fetch ─────────────────────────────────────────────────────────────
function loadData() {
  document.getElementById('hist-status').textContent = 'Loading…';
  fetch('/history.json?minutes=' + curMinutes)
    .then(r => r.json())
    .then(d => {
      const resTxt = d.res < 60 ? d.res + ' s' : (d.res / 60) + ' min';
      document.getElementById('hist-status').textContent =
        d.count + ' samples · ' + resTxt + ' resolution';
      renderAll(d);
    })
    .catch(e => {
      document.getElementById('hist-status').textContent = 'Error: ' + e;
    });
}

// ── Render all charts ──────────────────────────────────────────────────────
function renderAll(d) {
  drawChart('cT', [
    { label:'Sky',     color:'#a29bfe', data:d.sky,  lo:d.sky_lo,  hi:d.sky_hi  },
    { label:'Min',     color:'#74b9ff', data:d.fmin, lo:d.fmin_lo, hi:d.fmin_hi },
    { label:'Max',     color:'#fd79a8', data:d.fmax, lo:d.fmax_lo, hi:d.fmax_hi },
    { label:'Median',  color:'#55efc4', data:d.med,  lo:d.med_lo,  hi:d.med_hi  },
    { label:'Ambient', color:'#ffeaa7', data:d.amb,  lo:d.amb_lo,  hi:d.amb_hi  }
  ], d.t, d.now, '°C');

  drawChart('cC', [
    { label:'Cloud Mean',     color:'#dfe6e9', data:d.cloud,   lo:d.cloud_lo,   hi:d.cloud_hi   },
    { label:'Cloud Per-Pixel',color:'#b2bec3', data:d.cloudpx, lo:d.cloudpx_lo, hi:d.cloudpx_hi }
  ], d.t, d.now, '%');

  drawChart('cL', [
    { label:'Lux', color:'#fdcb6e', data:d.lux, lo:d.lux_lo, hi:d.lux_hi }
  ], d.t, d.now, 'lux');

  drawChart('cQ', [
    { label:'SQM', color:'#00cec9', data:d.sqm, lo:d.sqm_lo, hi:d.sqm_hi }
  ], d.t, d.now, 'mag/sq"');

  if (document.getElementById('cR')) drawRainChart('cR', d.rain, d.t, d.now);
}

// ── Rain / snow block chart ─────────────────────────────────────────────────
function drawRainChart(id, data, timestamps, nowMs) {
  const canvas = document.getElementById(id);
  if (!canvas) return;
  canvas.width = canvas.parentElement.clientWidth - 32;
  const W = canvas.width, H = canvas.height;
  const ctx = canvas.getContext('2d');
  const P = { t: 8, r: 14, b: 22, l: 54 };
  const cw = W - P.l - P.r, ch = H - P.t - P.b;

  ctx.fillStyle = '#0f3460';
  ctx.fillRect(0, 0, W, H);

  const n = timestamps ? timestamps.length : 0;
  if (n === 0 || !data) {
    ctx.fillStyle = '#888'; ctx.textAlign = 'center'; ctx.font = '13px sans-serif';
    ctx.fillText('No data yet – wait for the first 30-second bucket to close.', W / 2, H / 2);
    return;
  }

  const t0 = timestamps[0], t1 = timestamps[n - 1];
  const tSpan = (t1 - t0) || 1;
  const tx = i => P.l + (timestamps[i] - t0) / tSpan * cw;

  for (let i = 0; i < n; i++) {
    const v = data[i];
    if (v === null) continue;
    ctx.fillStyle = (v >= 0.5) ? '#e17055' : '#00b894';
    const x1 = tx(i);
    const x2 = (i + 1 < n) ? tx(i + 1) : P.l + cw;
    ctx.fillRect(x1, P.t, Math.max(x2 - x1, 1), ch);
  }

  // Y labels
  ctx.fillStyle = '#8899aa'; ctx.font = '10px monospace'; ctx.textAlign = 'right';
  ctx.fillText('Wet', P.l - 3, P.t + 9);
  ctx.fillText('Dry', P.l - 3, P.t + ch);

  // X-axis time labels
  const xTicks = 6;
  for (let k = 0; k <= xTicks; k++) {
    const xp = P.l + cw * k / xTicks;
    const tAt = t0 + tSpan * k / xTicks;
    const mAgo = (tAt - nowMs) / 60000;
    const lbl = (k === xTicks) ? 'now' :
                (Math.abs(mAgo) < 90 ? Math.round(-mAgo) + 'm' :
                                       (-mAgo / 60).toFixed(1) + 'h');
    ctx.fillStyle = '#8899aa'; ctx.textAlign = 'center'; ctx.font = '10px sans-serif';
    ctx.fillText(lbl, xp, P.t + ch + 14);
  }

  // Legend
  let lx = P.l;
  const ly = H - 2;
  ctx.font = '10px sans-serif'; ctx.textAlign = 'left';
  ctx.fillStyle = '#00b894'; ctx.fillRect(lx, ly - 8, 12, 8);
  ctx.fillStyle = '#ccc'; ctx.fillText('Dry', lx + 15, ly);
  lx += 45;
  ctx.fillStyle = '#e17055'; ctx.fillRect(lx, ly - 8, 12, 8);
  ctx.fillStyle = '#ccc'; ctx.fillText('Wet / Snow', lx + 15, ly);
}

// ── Chart renderer ─────────────────────────────────────────────────────────
function drawChart(id, series, timestamps, nowMs, yUnit) {
  const canvas = document.getElementById(id);
  if (!canvas) return;
  canvas.width = canvas.parentElement.clientWidth - 32;
  const W = canvas.width, H = canvas.height;
  const ctx = canvas.getContext('2d');
  const P = { t: 12, r: 14, b: 38, l: 54 };
  const cw = W - P.l - P.r, ch = H - P.t - P.b;

  // Background
  ctx.fillStyle = '#0f3460';
  ctx.fillRect(0, 0, W, H);

  const n = timestamps ? timestamps.length : 0;
  if (n === 0) {
    ctx.fillStyle = '#888'; ctx.textAlign = 'center';
    ctx.font = '13px sans-serif';
    ctx.fillText('No data yet – wait for the first 30-second bucket to close.',
                 W / 2, H / 2);
    return;
  }

  // X span in ms
  const t0 = timestamps[0], t1 = timestamps[n - 1];
  const tSpan = (t1 - t0) || 1;

  // Y range across all values (avg + lo + hi)
  let yMn = Infinity, yMx = -Infinity;
  for (const s of series) {
    for (const arr of [s.data, s.lo || [], s.hi || []]) {
      for (const v of arr) {
        if (v !== null && isFinite(v)) {
          if (v < yMn) yMn = v;
          if (v > yMx) yMx = v;
        }
      }
    }
  }
  if (!isFinite(yMn)) { yMn = 0; yMx = 1; }
  const ySpan = yMx - yMn || 1;
  yMn -= ySpan * 0.05; yMx += ySpan * 0.05;

  // Coordinate transforms
  const tx = i => P.l + (timestamps[i] - t0) / tSpan * cw;
  const ty = v => P.t + (1 - (v - yMn) / (yMx - yMn)) * ch;

  // Grid
  ctx.strokeStyle = '#2d3561'; ctx.lineWidth = 1;
  const yTicks = 4;
  for (let k = 0; k <= yTicks; k++) {
    const yp = P.t + ch * k / yTicks;
    ctx.beginPath(); ctx.moveTo(P.l, yp); ctx.lineTo(P.l + cw, yp); ctx.stroke();
    const val = yMx - (yMx - yMn) * k / yTicks;
    ctx.fillStyle = '#8899aa'; ctx.font = '10px monospace'; ctx.textAlign = 'right';
    ctx.fillText(val.toFixed(ySpan > 10 ? 0 : 1), P.l - 3, yp + 4);
  }

  const xTicks = 6;
  for (let k = 0; k <= xTicks; k++) {
    const xp = P.l + cw * k / xTicks;
    ctx.beginPath(); ctx.moveTo(xp, P.t); ctx.lineTo(xp, P.t + ch); ctx.stroke();
    const tAt  = t0 + tSpan * k / xTicks;
    const mAgo = (tAt - nowMs) / 60000;   // negative = past
    const lbl  = (k === xTicks) ? 'now' :
                 (Math.abs(mAgo) < 90 ? Math.round(-mAgo) + 'm' :
                                        (-mAgo / 60).toFixed(1) + 'h');
    ctx.fillStyle = '#8899aa'; ctx.textAlign = 'center'; ctx.font = '10px sans-serif';
    ctx.fillText(lbl, xp, P.t + ch + 14);
  }

  // Y-axis unit label (rotated)
  ctx.save();
  ctx.translate(11, P.t + ch / 2); ctx.rotate(-Math.PI / 2);
  ctx.fillStyle = '#8899aa'; ctx.font = '10px sans-serif'; ctx.textAlign = 'center';
  ctx.fillText(yUnit, 0, 0);
  ctx.restore();

  // Shaded lo/hi bands
  for (const s of series) {
    if (!s.lo || !s.hi) continue;
    ctx.fillStyle = s.color + '28';
    ctx.beginPath();
    let started = false;
    for (let i = 0; i < n; i++) {
      const v = s.lo[i];
      if (v === null) { started = false; continue; }
      if (!started) { ctx.moveTo(tx(i), ty(v)); started = true; }
      else ctx.lineTo(tx(i), ty(v));
    }
    for (let i = n - 1; i >= 0; i--) {
      const v = s.hi[i]; if (v !== null) ctx.lineTo(tx(i), ty(v));
    }
    ctx.closePath(); ctx.fill();
  }

  // Lines
  for (const s of series) {
    ctx.strokeStyle = s.color; ctx.lineWidth = 1.5;
    ctx.beginPath();
    let started = false;
    for (let i = 0; i < n; i++) {
      const v = s.data[i];
      if (v === null) { started = false; continue; }
      if (!started) { ctx.moveTo(tx(i), ty(v)); started = true; }
      else ctx.lineTo(tx(i), ty(v));
    }
    ctx.stroke();
  }

  // Legend along the bottom
  let lx = P.l;
  const ly = H - 8;
  ctx.font = '10px sans-serif'; ctx.textAlign = 'left';
  for (const s of series) {
    ctx.strokeStyle = s.color; ctx.lineWidth = 2;
    ctx.beginPath(); ctx.moveTo(lx, ly - 4); ctx.lineTo(lx + 14, ly - 4); ctx.stroke();
    ctx.fillStyle = '#ccc';
    ctx.fillText(s.label, lx + 17, ly);
    lx += 17 + ctx.measureText(s.label).width + 14;
  }
}

// ── Boot & auto-refresh ────────────────────────────────────────────────────
loadData();
setInterval(loadData, 30000);
</script>
)rawjs";

  html += "</body></html>";
  return html;
}

// ---------------------------------------------------------------------------
// Console page – live debug log viewer
// ---------------------------------------------------------------------------
inline String getConsolePage()
{
  String html = getPageHeader("Console – " SERVER_NAME);
  html += getNavBar();

  html +=
    "<div class='card'>\n"
    "<h2 style='margin-top:0'>Debug Console</h2>\n"
    "<div style='margin-bottom:8px;display:flex;align-items:center;gap:8px;flex-wrap:wrap;'>\n"
    "  <button id='btn-pause' class='tbtn'>Pause</button>\n"
    "  <button id='btn-clear' class='tbtn'>Clear</button>\n"
    "  <button id='btn-copy'  class='tbtn'>Copy</button>\n"
    "  <span id='con-status' style='font-size:0.8em;color:#636e72'>Polling every 2 s</span>\n"
    "</div>\n"
    "<div id='log' style='"
      "height:520px;overflow-y:auto;background:#0d1117;border-radius:4px;"
      "padding:10px;font-family:monospace;font-size:0.83em;line-height:1.55;"
      "white-space:pre-wrap;word-break:break-all;"
    "'></div>\n"
    "</div>\n";

  html += R"rawjs(
<style>
.le  { margin: 0; }
.ts  { color: #636e72; user-select: none; }
.rep { color: #fd79a8; font-style: italic; }
</style>
<script>
function esc(s){
  return s.replace(/&/g,'&amp;').replace(/</g,'&lt;').replace(/>/g,'&gt;');
}
function fmtMs(ms){
  var h=Math.floor(ms/3600000),
      m=Math.floor((ms%3600000)/60000),
      s=Math.floor((ms%60000)/1000);
  return [h,m,s].map(function(x){return String(x).padStart(2,'0');}).join(':');
}

var lastSeq=-1, paused=false;

function render(entries){
  var el=document.getElementById('log');
  var atBottom=(el.scrollHeight-el.scrollTop-el.clientHeight)<40;
  el.innerHTML='';
  for(var i=0;i<entries.length;i++){
    var e=entries[i];
    var rep=e.n>1?' <span class="rep">(\xd7'+e.n+')</span>':'';
    var d=document.createElement('div');
    d.className='le';
    d.innerHTML='<span class="ts">['+fmtMs(e.ms)+']</span> '+esc(e.msg)+rep;
    el.appendChild(d);
  }
  if(atBottom) el.scrollTop=el.scrollHeight;
}

function poll(){
  if(paused) return;
  fetch('/console.json').then(function(r){return r.json();}).then(function(d){
    if(d.seq!==lastSeq){lastSeq=d.seq;render(d.entries);}
    document.getElementById('con-status').textContent=
      'Last update: '+new Date().toLocaleTimeString()+' \u2022 '+d.entries.length+' lines';
  }).catch(function(){});
}

document.getElementById('btn-pause').onclick=function(){
  paused=!paused;
  this.textContent=paused?'Resume':'Pause';
  this.style.background=paused?'#c0392b':'';
};
document.getElementById('btn-clear').onclick=function(){
  document.getElementById('log').innerHTML='';
  lastSeq=-1;
};
document.getElementById('btn-copy').onclick=function(){
  var lines=document.querySelectorAll('#log .le');
  var text=Array.from(lines).map(function(el){return el.innerText;}).join('\n');
  var btn=this;
  navigator.clipboard.writeText(text).then(function(){
    btn.textContent='Copied!';
    setTimeout(function(){btn.textContent='Copy';},1500);
  }).catch(function(){
    btn.textContent='Failed';
    setTimeout(function(){btn.textContent='Copy';},1500);
  });
};

setInterval(poll,2000);
poll();
</script>
)rawjs";

  html += "</body></html>";
  return html;
}

#endif // HTML_TEMPLATES_H
